Faust-Lighting/Horticulture_Light_EQ_3-Band/mechanical files/asm1001 rev 0.2/ASM1001 Rev 0.2 SOLIDWORKS/PWR1003.SLDPRT

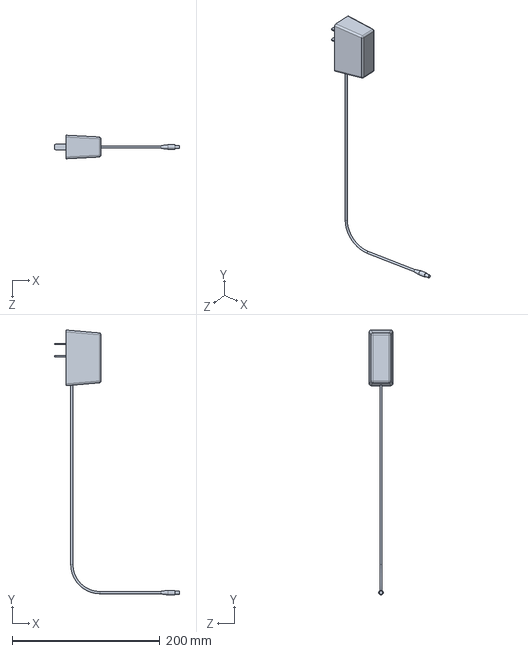
[picture p23: CAD file, 2017-03-16]
mechanical files/asm1001 rev 0.2/ASM1001 Rev 0.2 SOLIDWORKS/PWR1003.SLDPRT
169.9 x 358.8 x 32.0 mm
