Faust-Lighting/Horticulture_Light_EQ_3-Band/mechanical files/asm1001 rev 0.2/ASM1001 Rev 0.2 SOLIDWORKS/HSG1001-1.sldprt

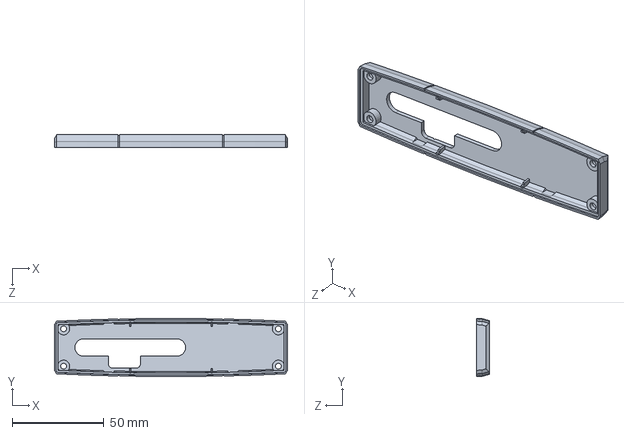
[picture p24: CAD file, 2017-03-16]
mechanical files/asm1001 rev 0.2/ASM1001 Rev 0.2 SOLIDWORKS/HSG1001-1.sldprt
127.0 x 31.8 x 6.86 mm
