Faust-Lighting/Horticulture_Light_EQ_3-Band/mechanical files/asm1001 rev 0.2/ASM1001 Rev 0.2 SOLIDWORKS/FST1001.SLDPRT

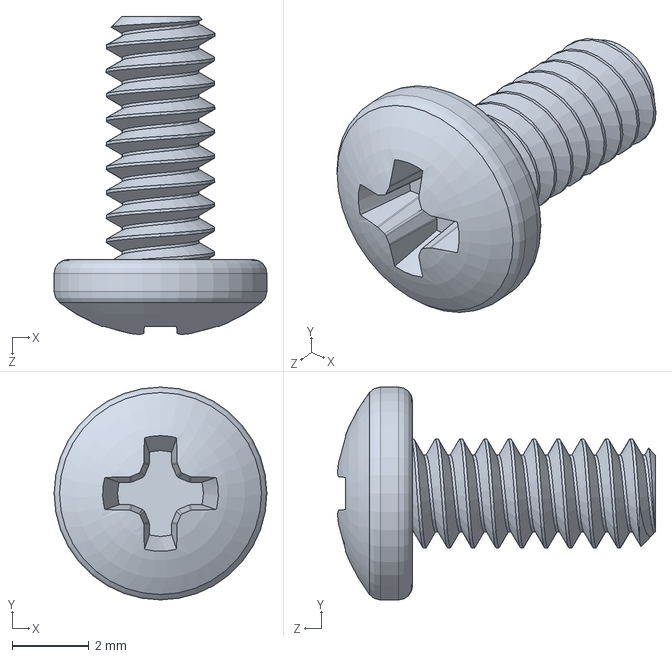
[picture p25: CAD file, 2017-03-16]
mechanical files/asm1001 rev 0.2/ASM1001 Rev 0.2 SOLIDWORKS/FST1001.SLDPRT
5.56 x 5.56 x 8.31 mm
