Faust-Lighting/Horticulture_Light_EQ_3-Band/mechanical files/asm1001 rev 0.2/ASM1001 Rev 0.2 SOLIDWORKS/MIS1003-1.SLDPRT

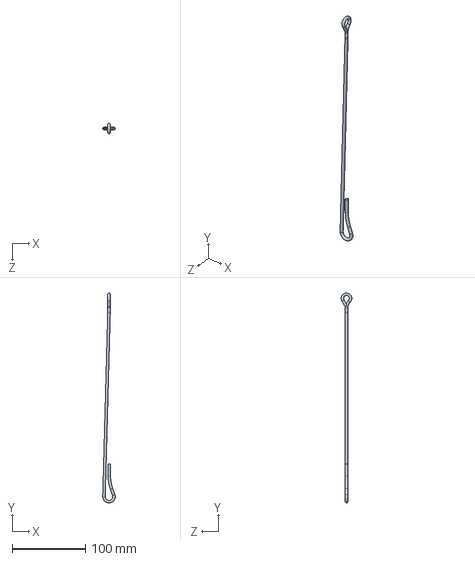
[picture p26: CAD file, 2017-03-16]
mechanical files/asm1001 rev 0.2/ASM1001 Rev 0.2 SOLIDWORKS/MIS1003-1.SLDPRT
17.2 x 286.1 x 14.7 mm
