Faust-Lighting/Horticulture_Light_EQ_3-Band/mechanical files/asm1001 rev 0.2/ASM1001 Rev 0.2 SOLIDWORKS/PCB1002.SLDPRT

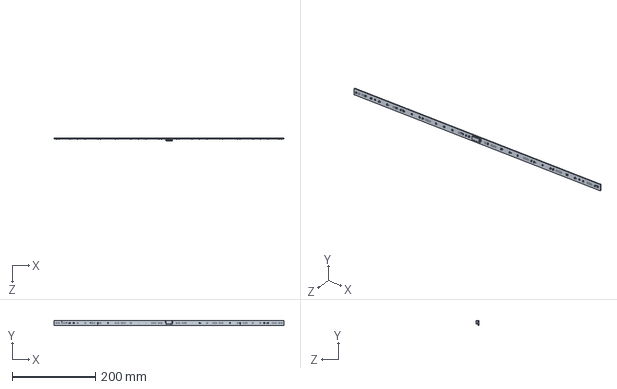
[picture p27: CAD file, 2017-03-16]
mechanical files/asm1001 rev 0.2/ASM1001 Rev 0.2 SOLIDWORKS/PCB1002.SLDPRT
551.2 x 12.8 x 6.60 mm
