Faust-Lighting/Horticulture_Light_EQ_3-Band/mechanical files/asm1001 rev 0.2/ASM1001 Rev 0.2 SOLIDWORKS/MIS1003-3.SLDPRT

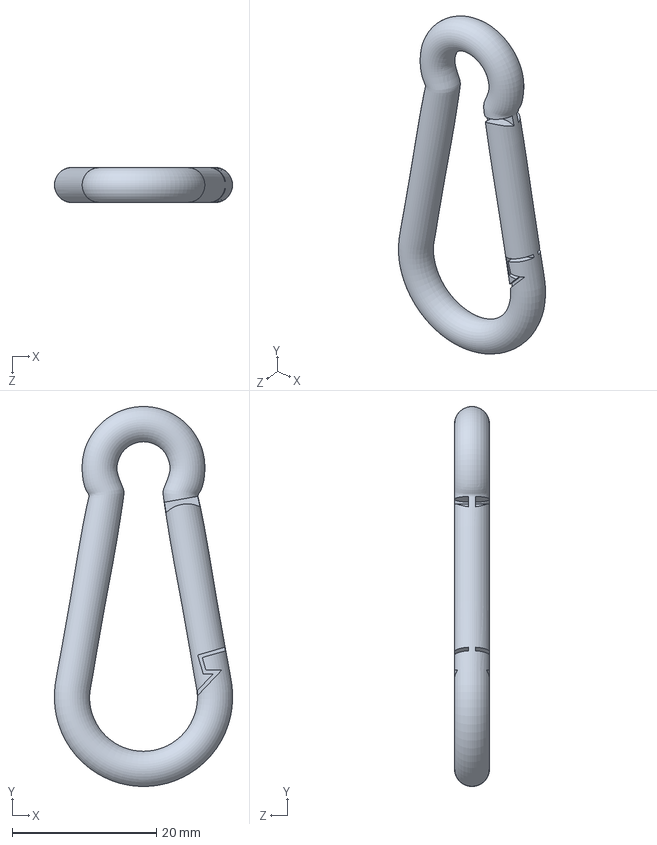
[picture p29: CAD file, 2017-03-16]
mechanical files/asm1001 rev 0.2/ASM1001 Rev 0.2 SOLIDWORKS/MIS1003-3.SLDPRT
24.7 x 52.6 x 4.88 mm
